HamTomo/Hubsan/104L/IMG_3484D.JPG

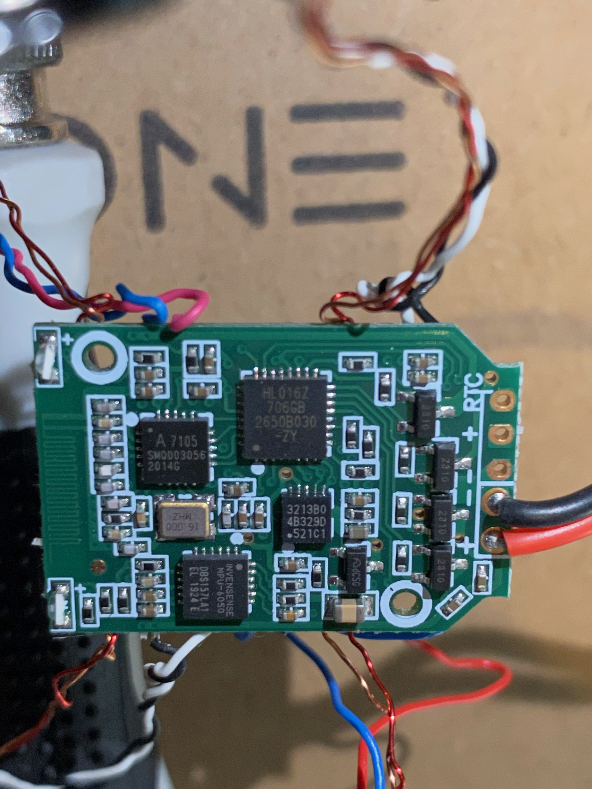
104L/IMG_3484D.JPG
