HamTomo/Hubsan/104L/IMG_3485D.JPG

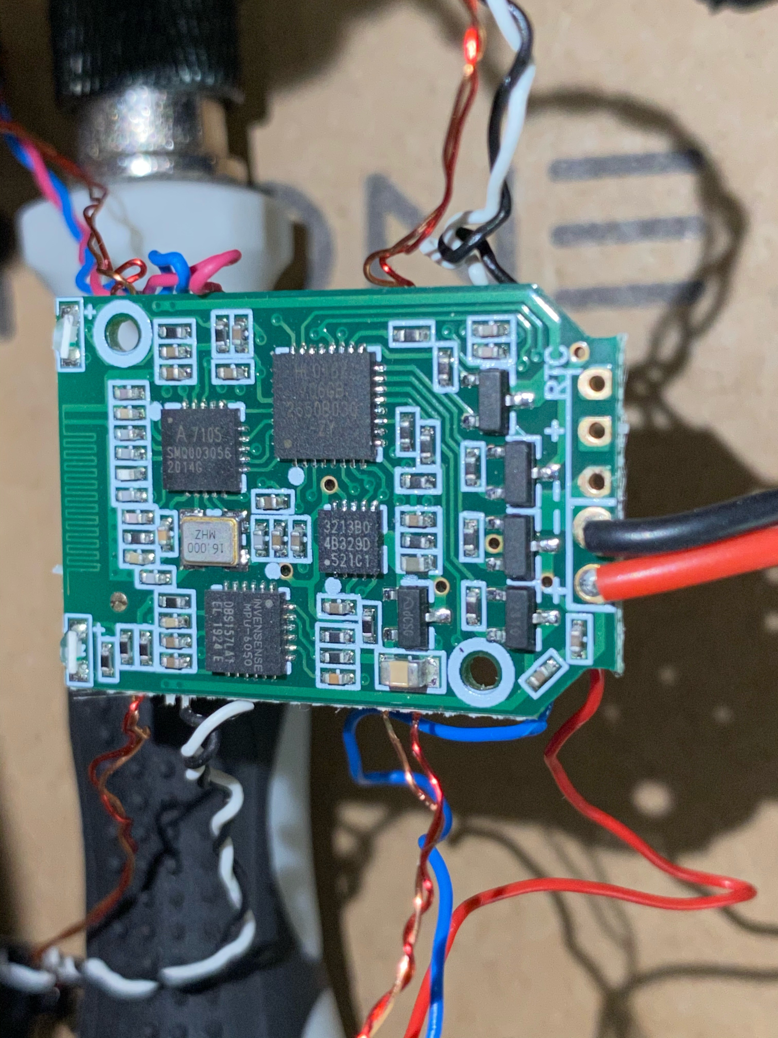
104L/IMG_3485D.JPG
