HamTomo/Hubsan/104L/IMG_3486D.JPG

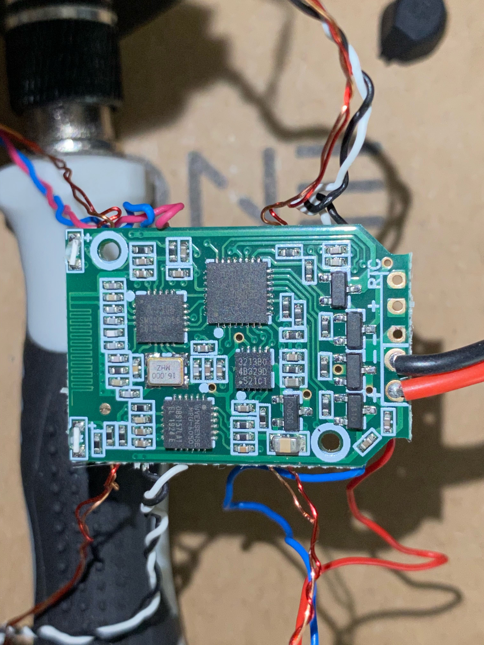
104L/IMG_3486D.JPG
