HamTomo/Hubsan/104L/IMG_3487D.JPG

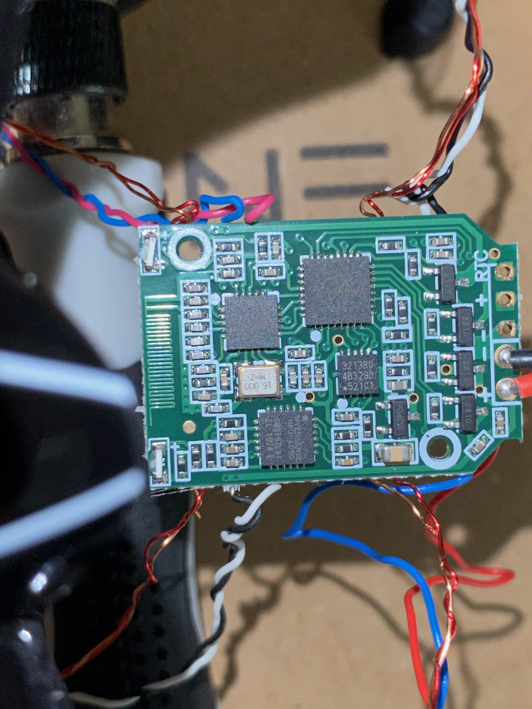
104L/IMG_3487D.JPG
