HamTomo/Hubsan/104L/IMG_3488D.JPG

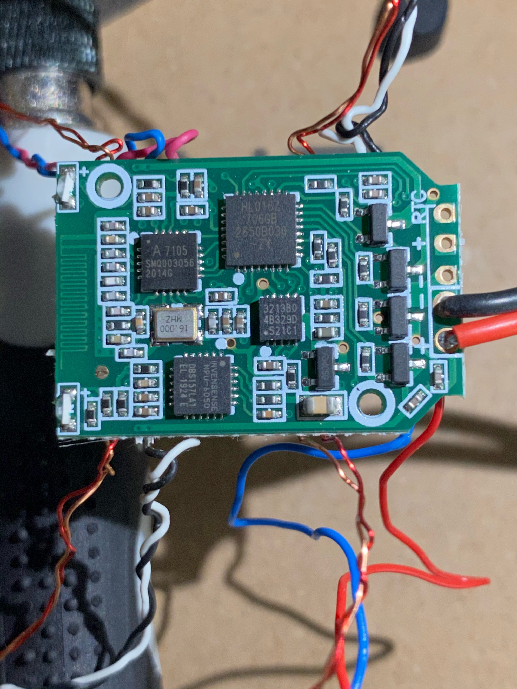
104L/IMG_3488D.JPG
