HamTomo/Hubsan/104L/IMG_3489D.JPG

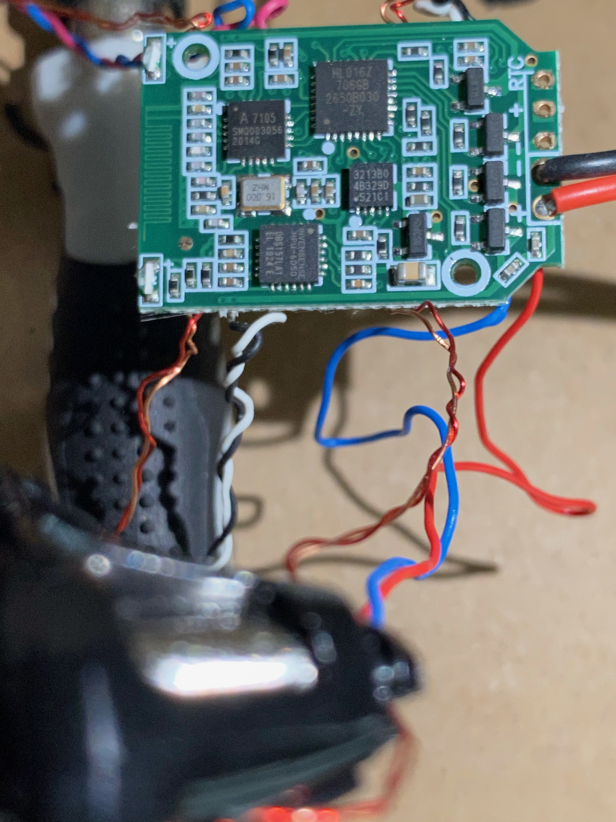
104L/IMG_3489D.JPG
