HamTomo/Hubsan/104L/IMG_3490D.JPG

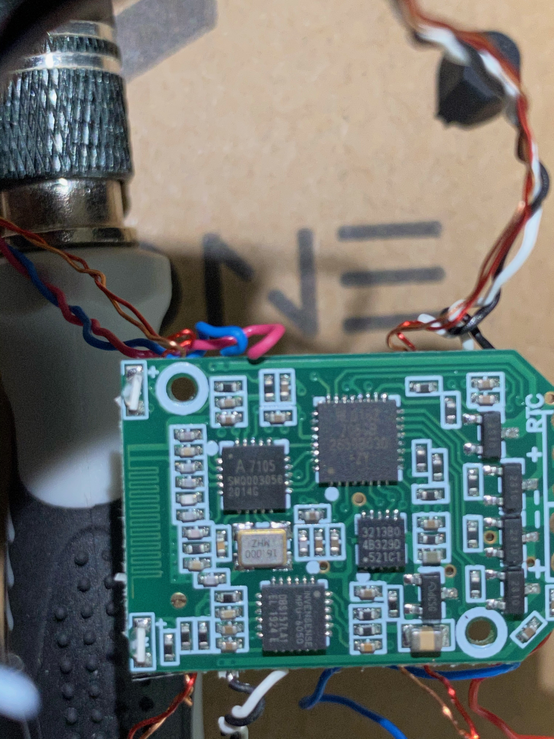
104L/IMG_3490D.JPG
