HamTomo/Hubsan/104L/IMG_3491D.JPG

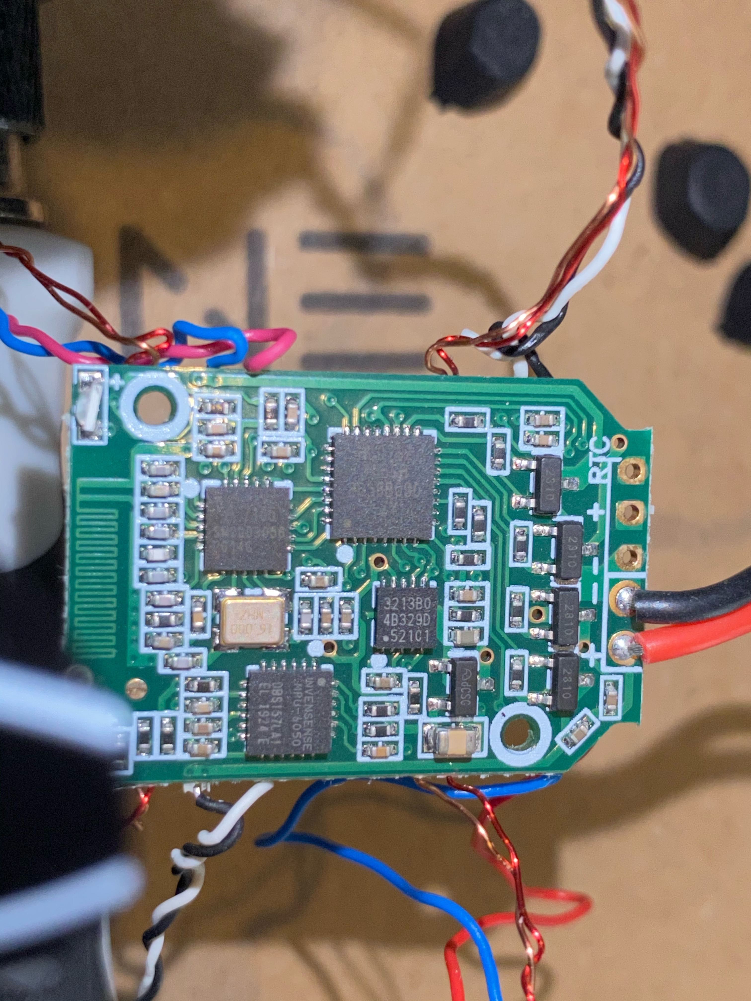
104L/IMG_3491D.JPG
