HamTomo/Hubsan/104L/IMG_3492D.JPG

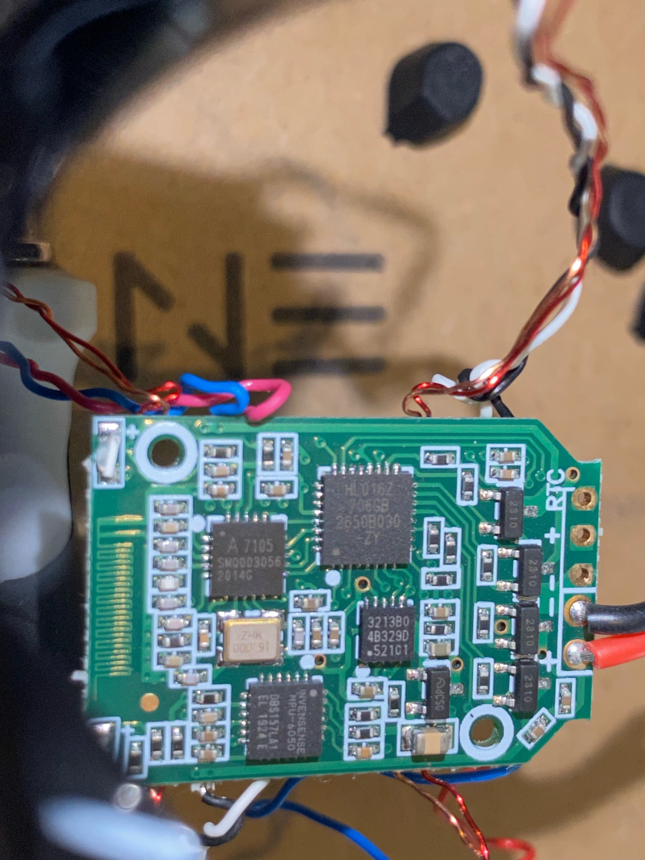
104L/IMG_3492D.JPG
