HamTomo/Hubsan/104L/IMG_3493D.JPG

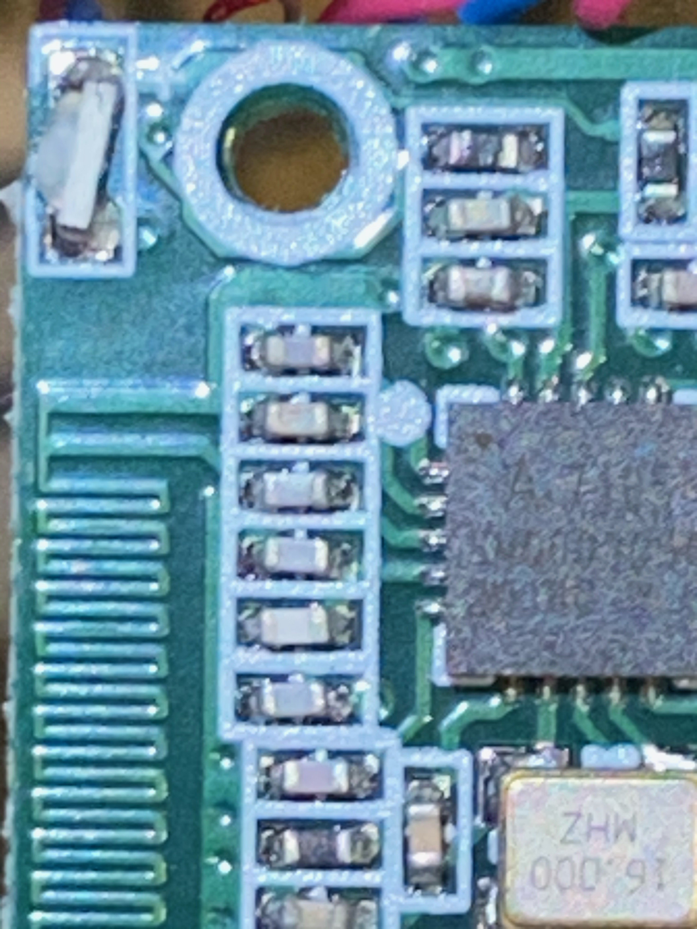
104L/IMG_3493D.JPG
