HamTomo/Hubsan/104L/IMG_3494D.JPG

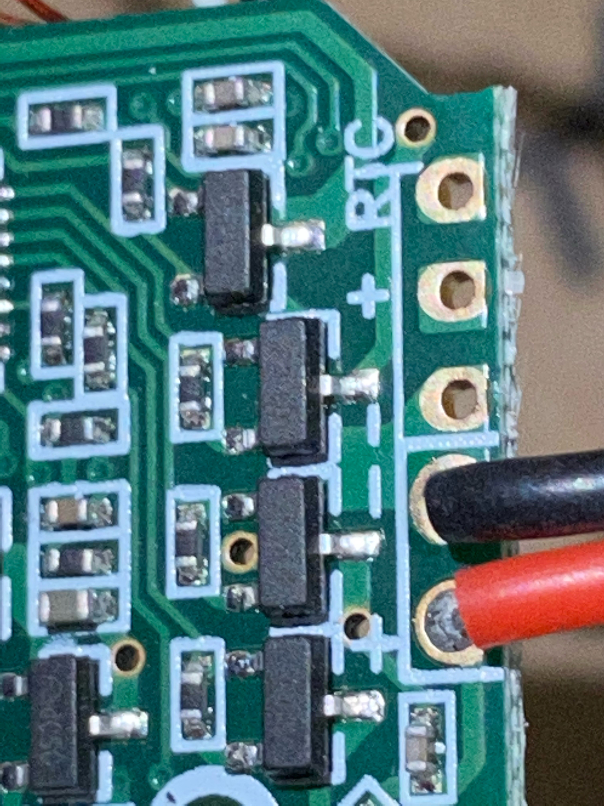
104L/IMG_3494D.JPG
