HamTomo/Hubsan/104L/IMG_3496D.JPG

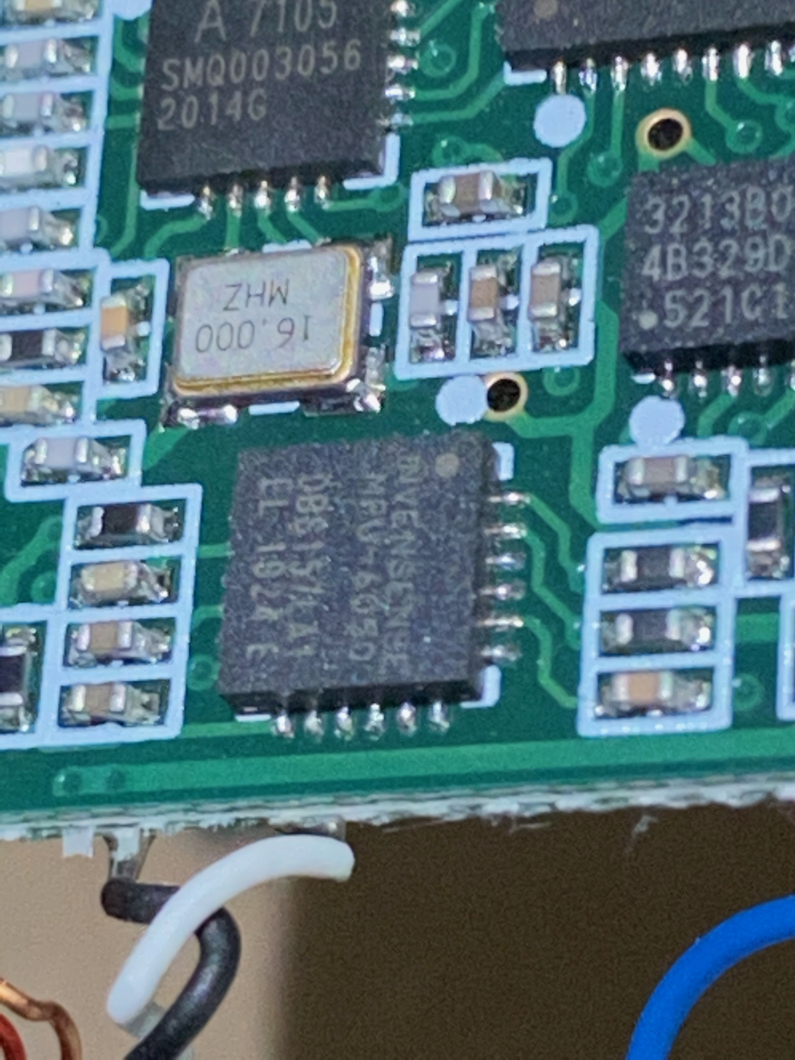
104L/IMG_3496D.JPG
