HamTomo/Hubsan/104L/IMG_3500D.JPG

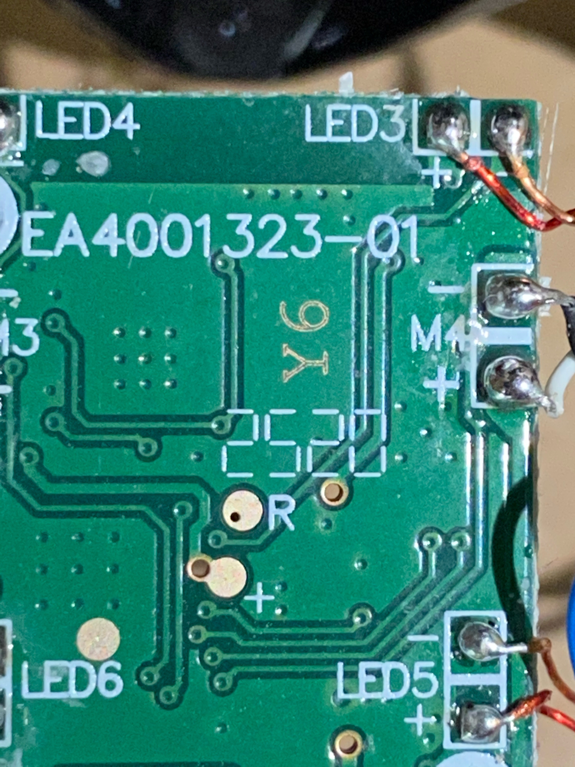
104L/IMG_3500D.JPG
