HamTomo/Hubsan/104L/IMG_3501D.JPG

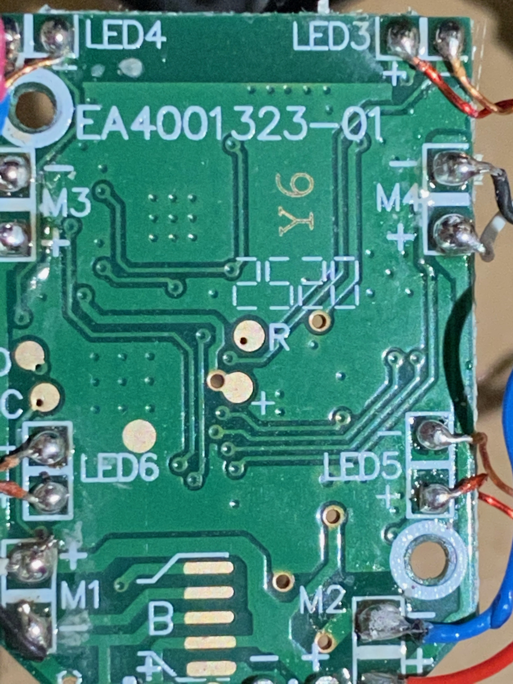
104L/IMG_3501D.JPG
