HamTomo/Hubsan/104L/IMG_3502D.JPG

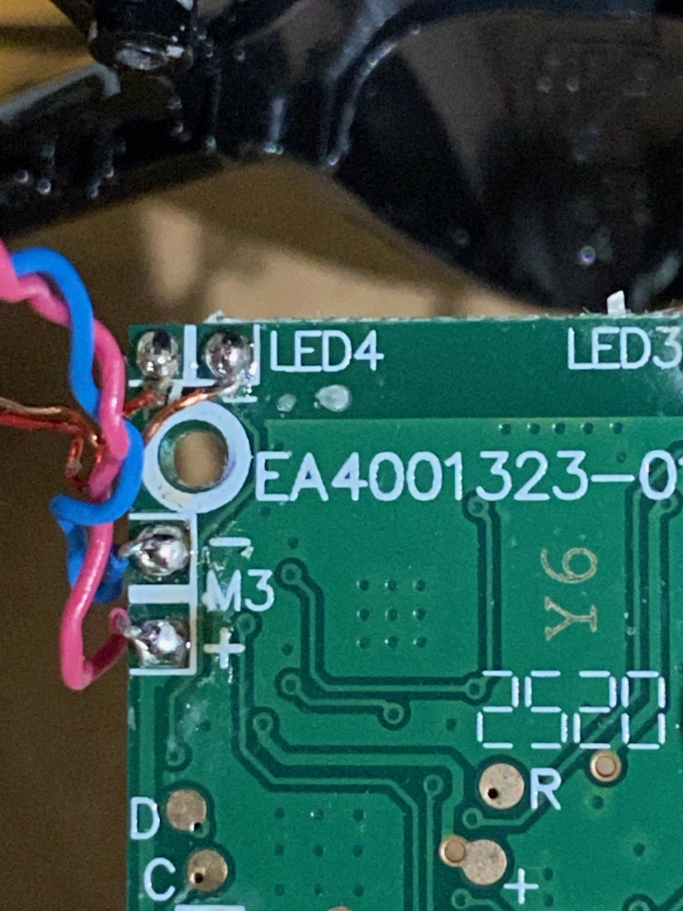
104L/IMG_3502D.JPG
