HamTomo/Hubsan/104L/IMG_3503D.JPG

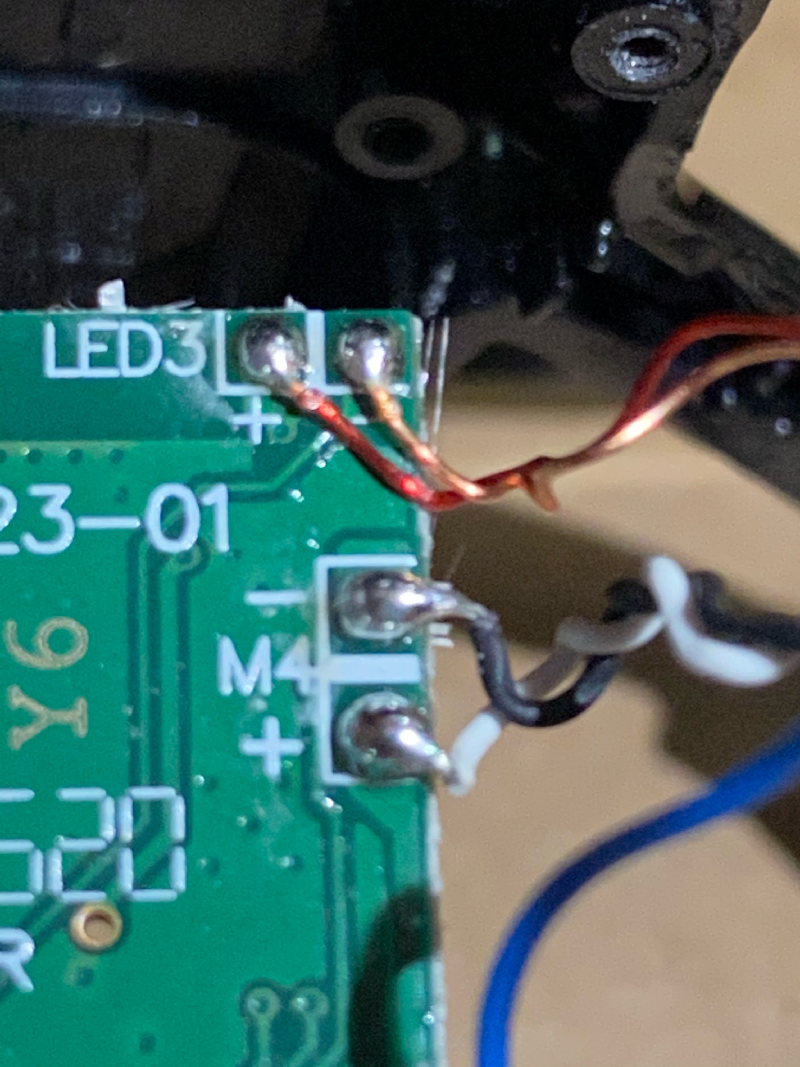
104L/IMG_3503D.JPG
