HamTomo/Hubsan/TX/IMG_3475.JPG

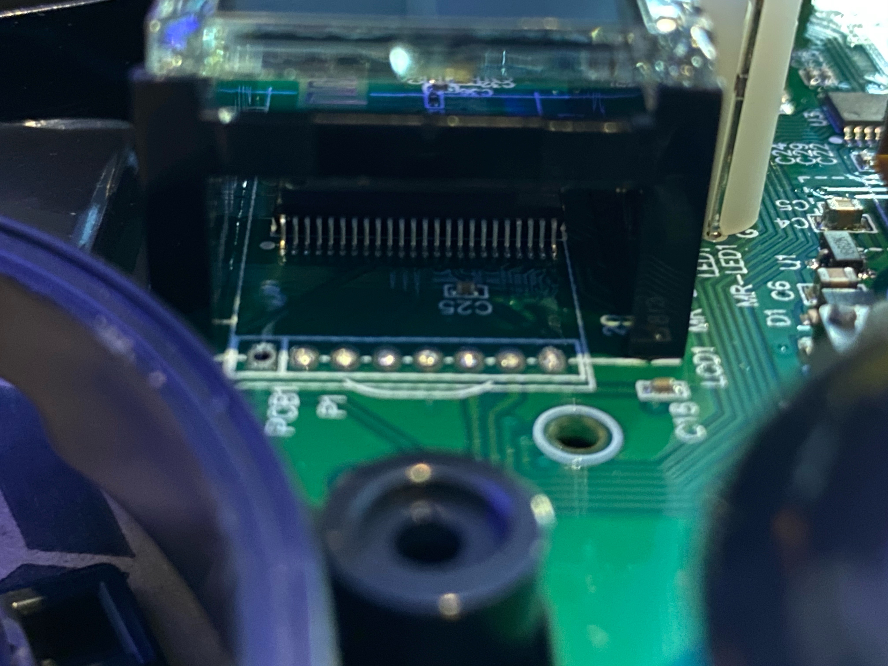
TX/IMG_3475.JPG
