HamTomo/Hubsan/TX/IMG_3476D.JPG

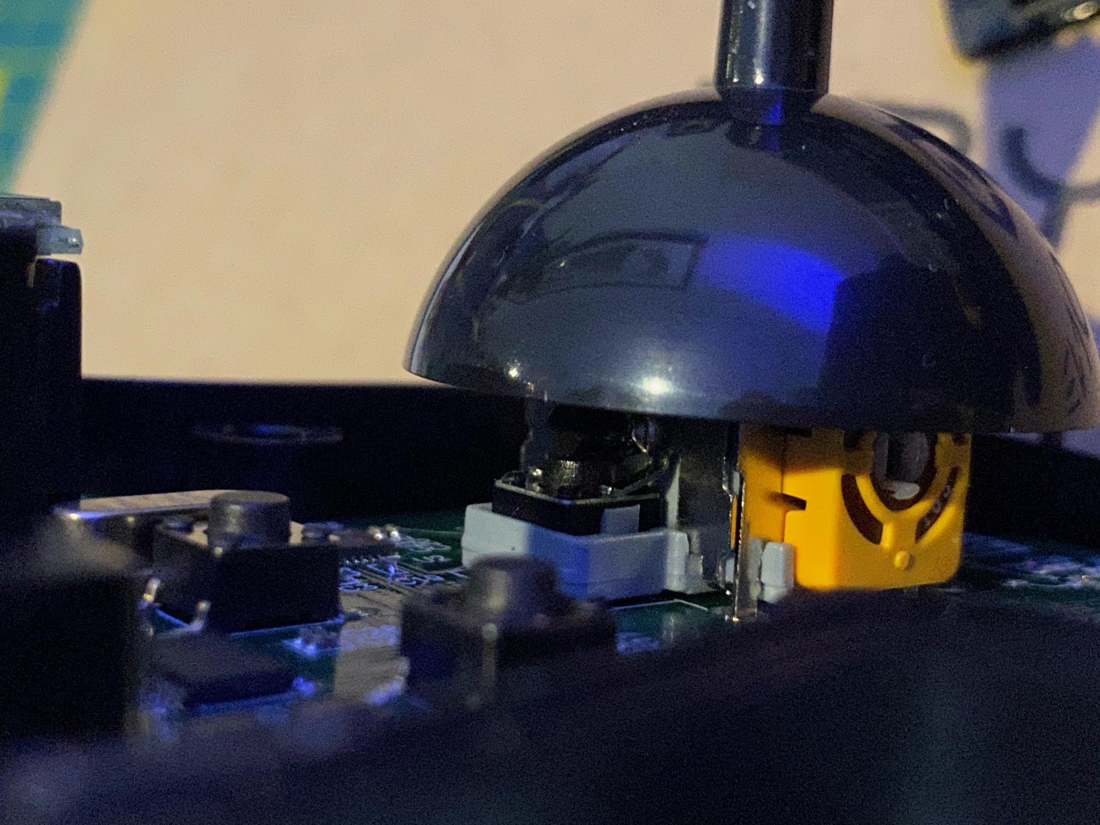
TX/IMG_3476D.JPG
