HamTomo/Hubsan/TX/IMG_3477D.JPG

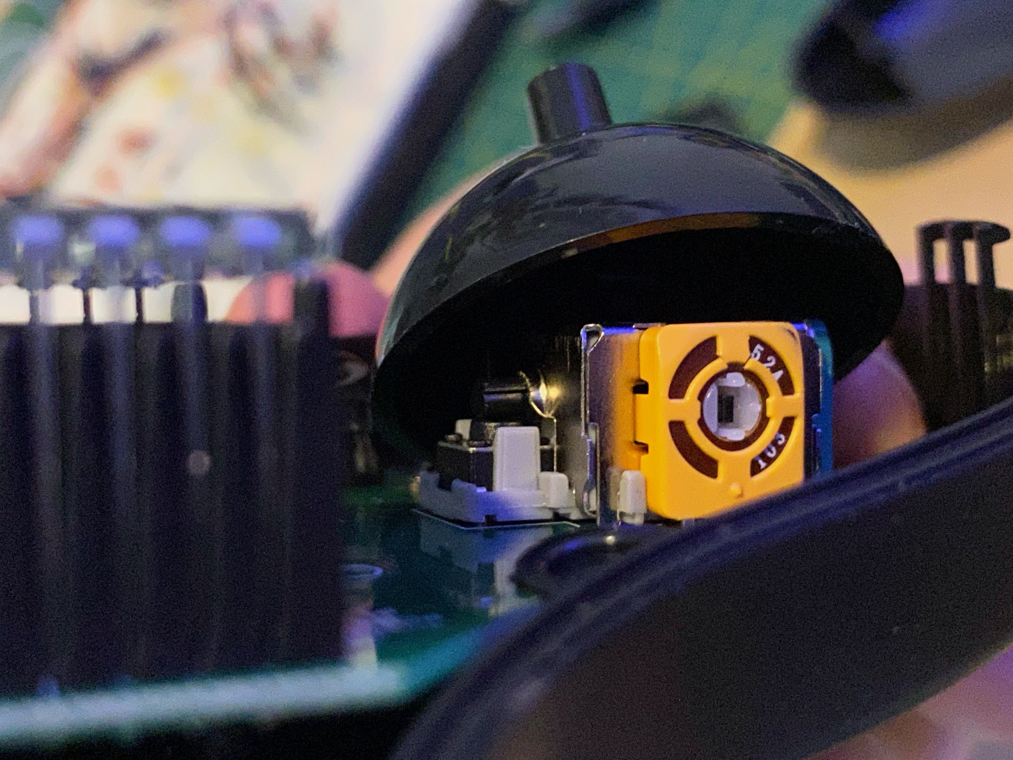
TX/IMG_3477D.JPG
