HamTomo/Hubsan/104L/IMG_3482D.JPG

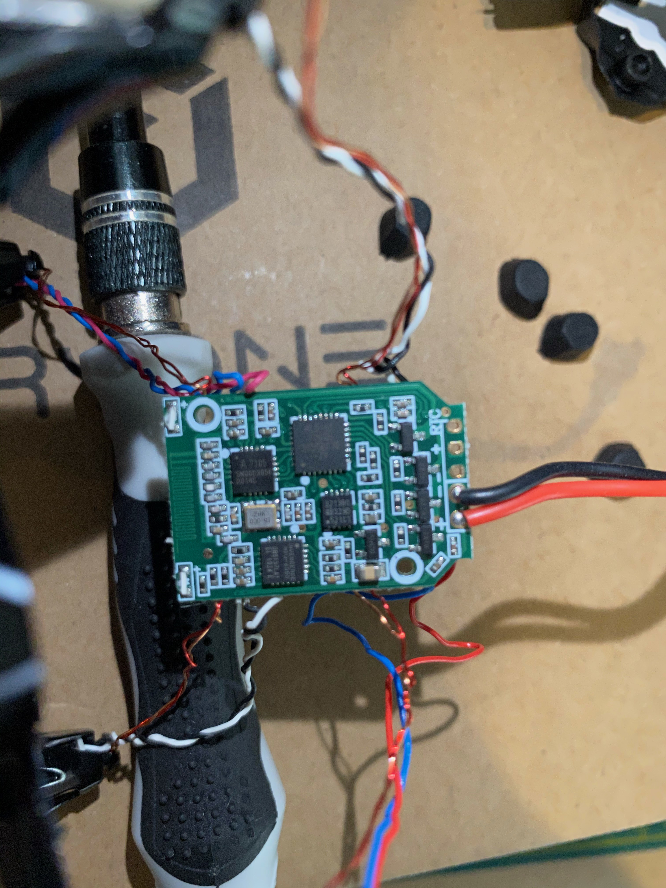
104L/IMG_3482D.JPG
