HamTomo/Hubsan/104L/IMG_3483D.JPG

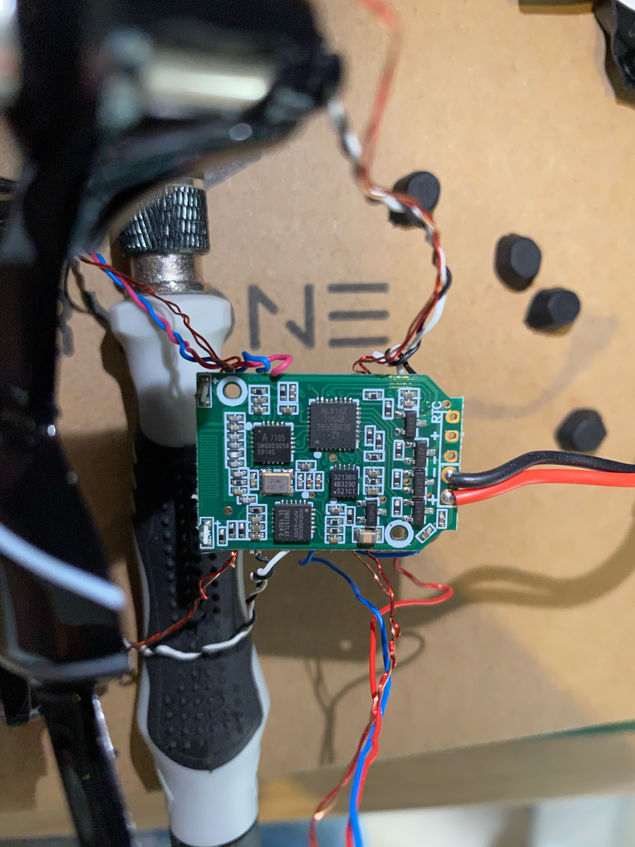
104L/IMG_3483D.JPG
