HamTomo/Hubsan/104L/IMG_3498D.JPG

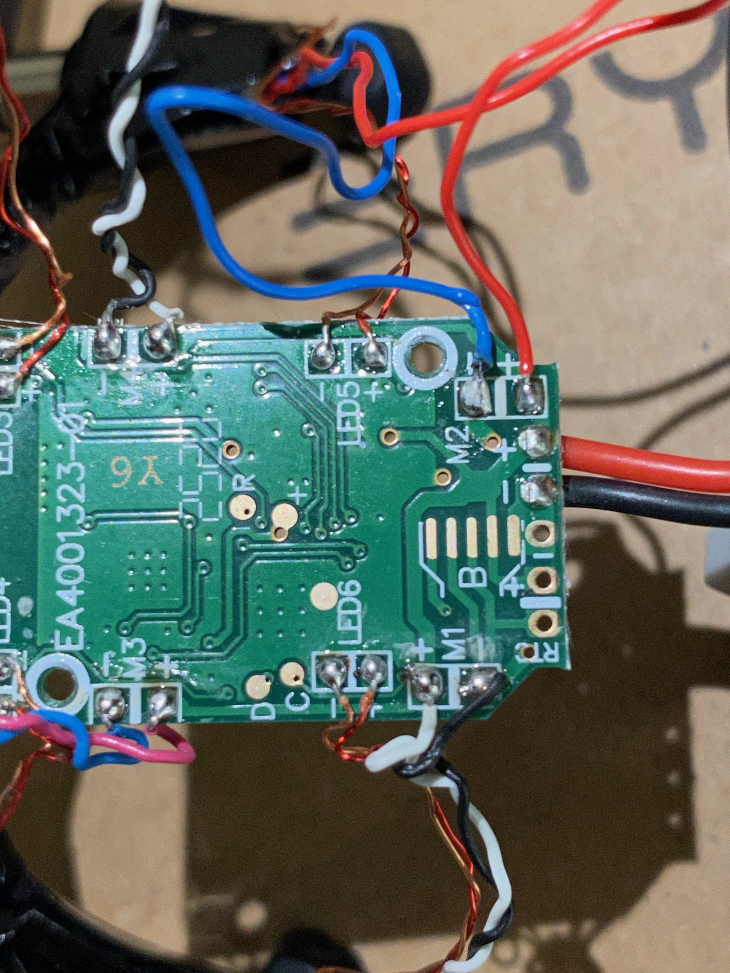
104L/IMG_3498D.JPG
