HamTomo/Hubsan/TX/IMG_3463D.JPG

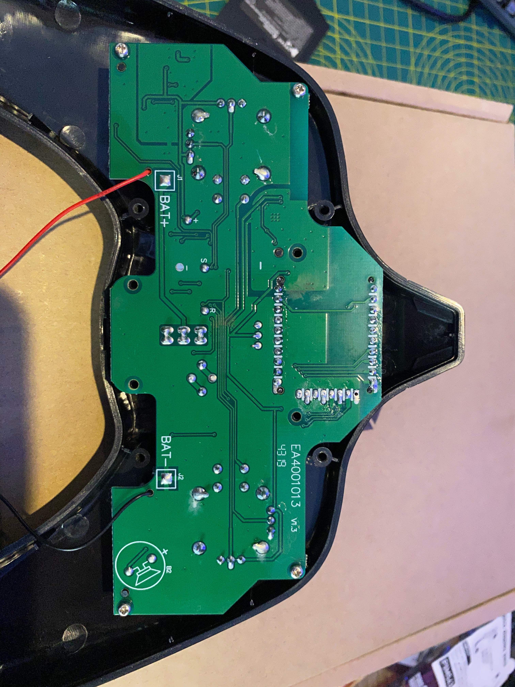
TX/IMG_3463D.JPG
