HamTomo/Hubsan/TX/IMG_3464D.JPG

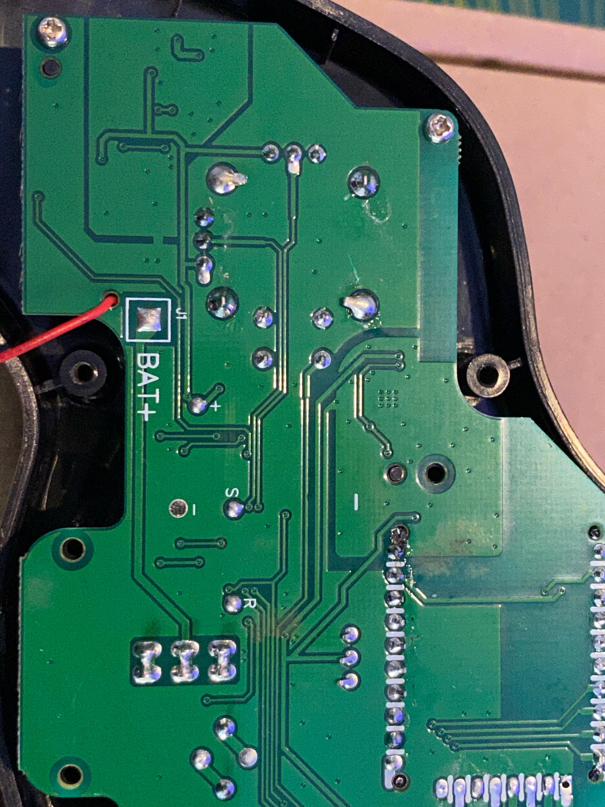
TX/IMG_3464D.JPG
