HamTomo/Hubsan/TX/IMG_3465D.JPG

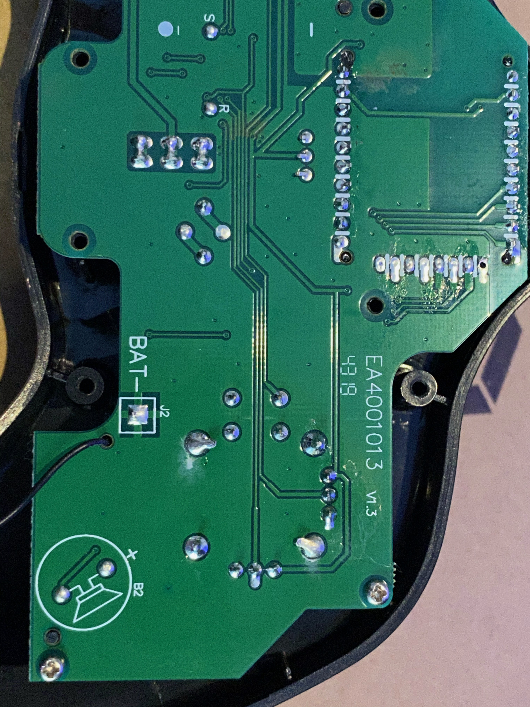
TX/IMG_3465D.JPG
