HamTomo/Hubsan/TX/IMG_3466D.JPG

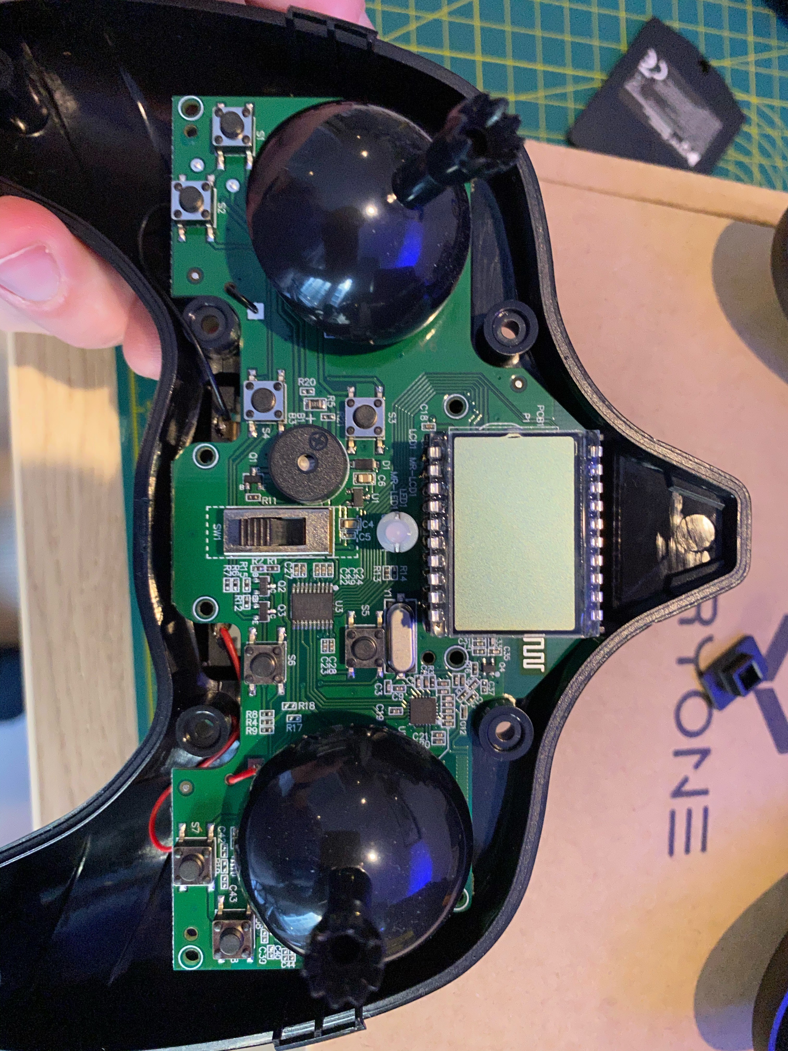
TX/IMG_3466D.JPG
