HamTomo/Hubsan/TX/IMG_3467D.JPG

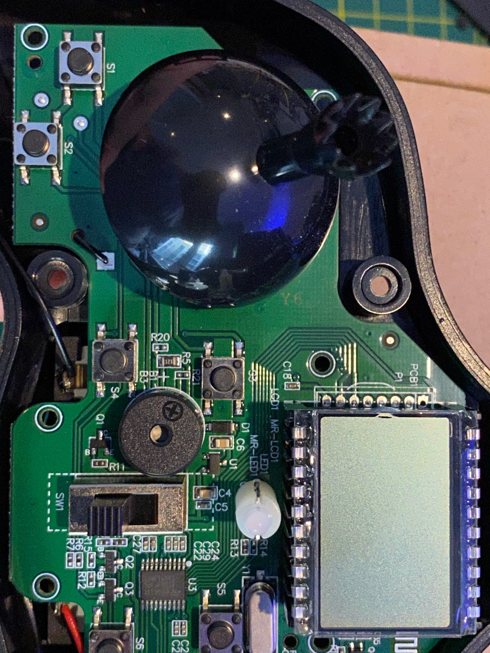
TX/IMG_3467D.JPG
