HamTomo/Hubsan/TX/IMG_3468D.JPG

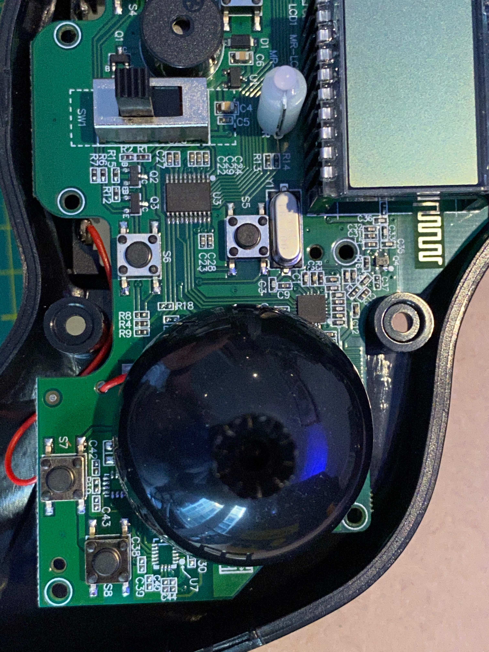
TX/IMG_3468D.JPG
