HamTomo/Hubsan/TX/IMG_3469D.JPG

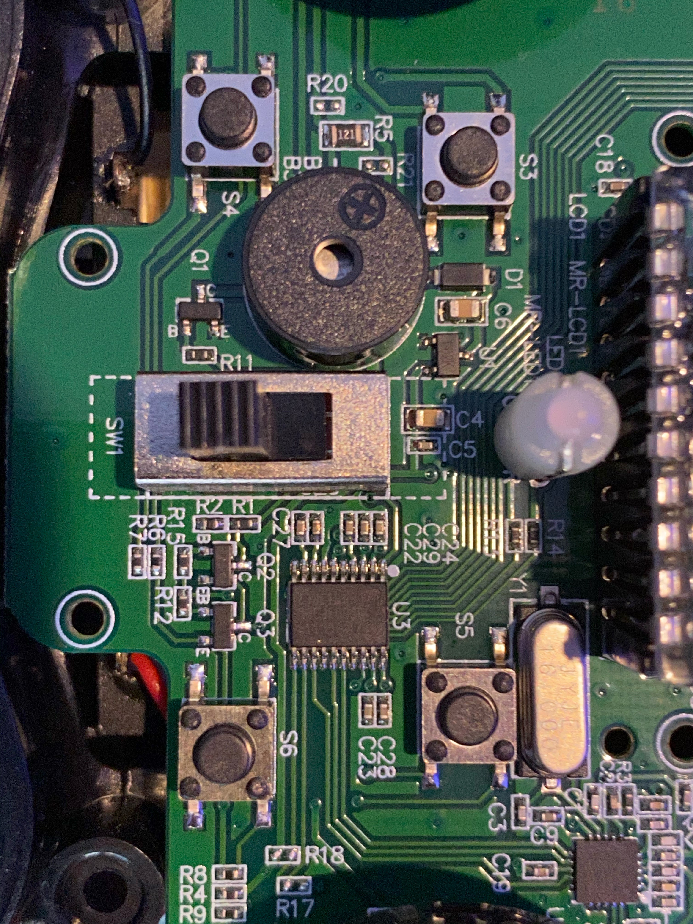
TX/IMG_3469D.JPG
