HamTomo/Hubsan/TX/IMG_3470D.JPG

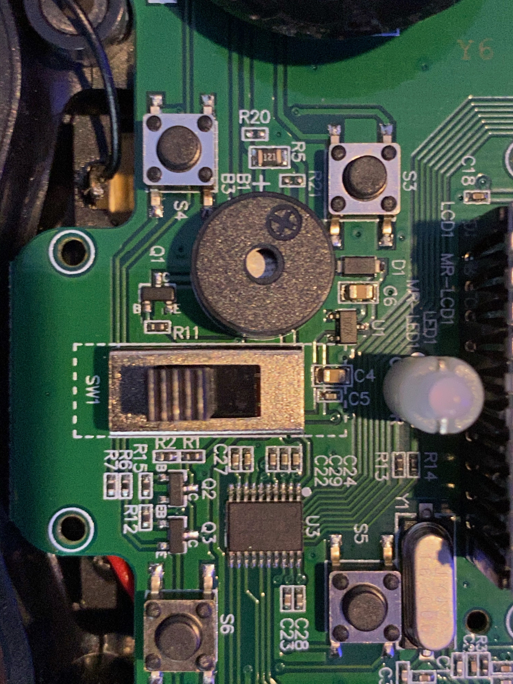
TX/IMG_3470D.JPG
