HamTomo/Hubsan/TX/IMG_3472D.JPG

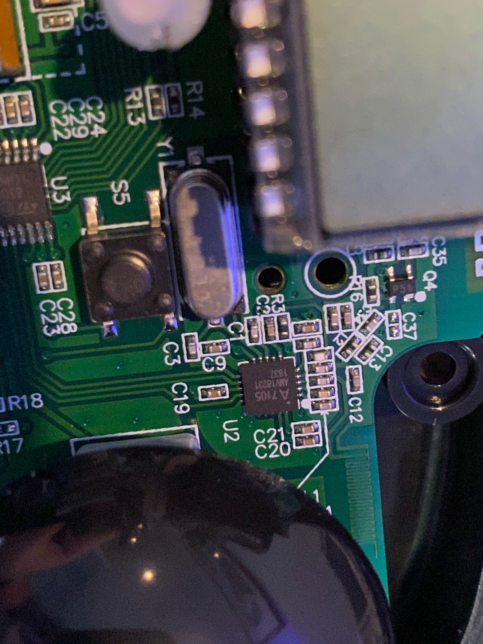
TX/IMG_3472D.JPG
