HamTomo/Hubsan/TX/IMG_3473D.JPG

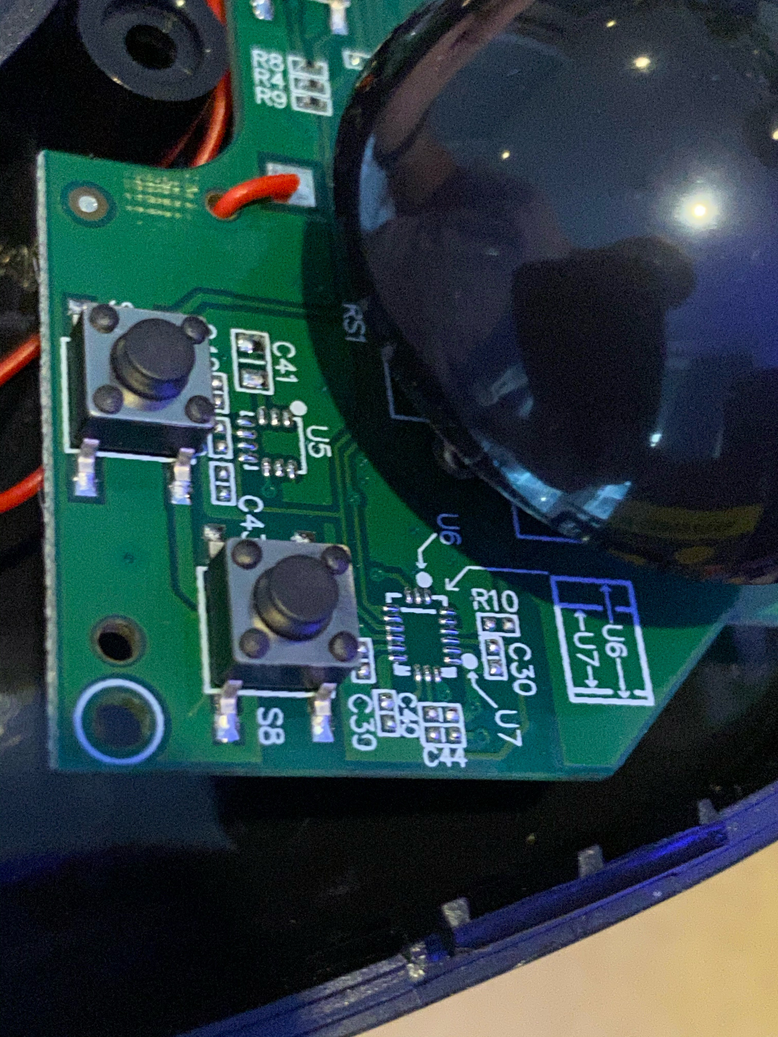
TX/IMG_3473D.JPG
