HamTomo/Hubsan/TX/IMG_3474D.JPG

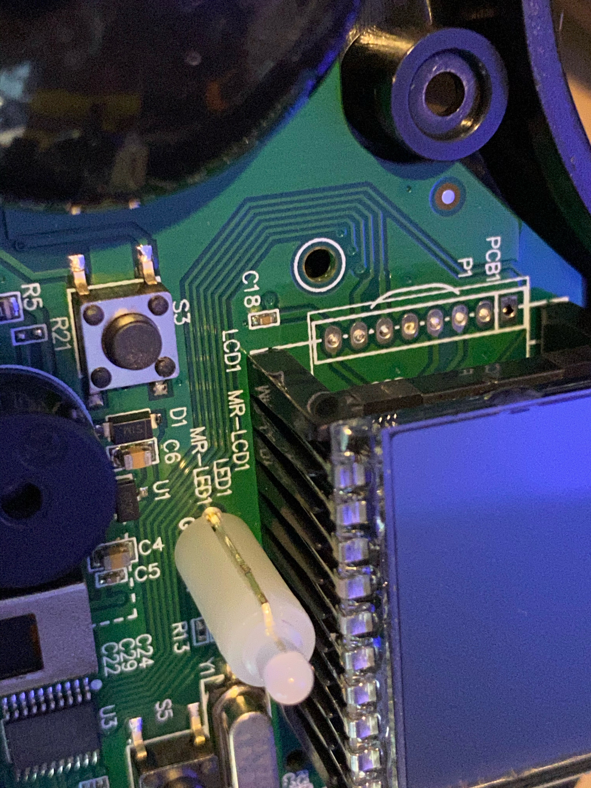
TX/IMG_3474D.JPG
